Circuit-Digest/EdgeSense/X-CUBE-AI/App/gesture_nn_data_params.c

/**
  ******************************************************************************
  * @file    gesture_nn_data_params.c
  * @author  AST Embedded Analytics Research Platform
  * @date    2026-09-09T18:25:11+0530
  * @brief   AI Tool Automatic Code Generator for Embedded NN computing
  ******************************************************************************
  * Copyright (c) 2026 STMicroelectronics.
  * All rights reserved.
  *
  * This software is licensed under terms that can be found in the LICENSE file
  * in the root directory of this software component.
  * If no LICENSE file comes with this software, it is provided AS-IS.
  ******************************************************************************
  */

#include "gesture_nn_data_params.h"


/**  Activations Section  ****************************************************/
ai_handle g_gesture_nn_activations_table[1 + 2] = {
  AI_HANDLE_PTR(AI_MAGIC_MARKER),
  AI_HANDLE_PTR(NULL),
  AI_HANDLE_PTR(AI_MAGIC_MARKER),
};




/**  Weights Section  ********************************************************/
AI_ALIGNED(32)
const ai_u64 s_gesture_nn_weights_array_u64[5555] = {
  0xbd9bb6e83f14df5fU, 0xbd44f94dbe014eacU, 0xbd1a51113dd24123U, 0xbcd553593df90affU,
  0x3d6153e93e846b70U, 0xbe80cb583c3d5268U, 0xbdba1bb5bd9777c5U, 0x3f04b9d13dfc55edU,
  0x3bf491773cfa8731U, 0x3c975adabdd268f2U, 0x3b5d58443d19daa8U, 0xbcabd6d23dd9a1a6U,
  0xbdf308f43df9d848U, 0x3d3f640bbe3ce48dU, 0xbd5397b7bd332f07U, 0xbdb320333e840855U,
  0xbe5b8785be28c286U, 0x3c8ddacebdc4873fU, 0xbdaa8765bc5651dfU, 0xbdf82327be15460fU,
  0xbe254b2fbda32cbeU, 0xbdf089a43c857d3dU, 0x3eed92773d64c81dU, 0xbd1e19433d0020d6U,
  0xbc7e3dd33d837038U, 0xbd4f8ecd3ca2f35dU, 0xbe0b01223d28c61bU, 0xbe108f2dbce864bcU,
  0xbc1e46f0be5d9a9fU, 0xbe22220bbe2b8cdcU, 0x3d86b2283e4858aeU, 0xbdf83359bd084633U,
  0x3d54fd3c3c97acfaU, 0xbd25b1a83d59f5f9U, 0xbd9daabcbda7d2eaU, 0xbe33ac22be445608U,
  0xbd978d073d9d0282U, 0x3e51d1833e2aa8e3U, 0xbc61f3f13dbe44bfU, 0xbc63d6b13cd2e7aaU,
  0xbdb214d6bd10411eU, 0x3e357c22be07b82eU, 0xbe528ac13d65b2efU, 0xbe2cf3c0be321670U,
  0xbd25f38fbdc2d10aU, 0xbb11bd8e3e0925a0U, 0x3d5b9c55bc33f40bU, 0x3d4cb53e3dd98429U,
  0xbd83e82f3d1fc662U, 0xbe38ffffbd22bc52U, 0xbea0b887be0b6427U, 0xbe7a15d0be7af064U,
  0x3ec2225cbe8b4523U, 0xbcadbf9d3e7c4e67U, 0x3e2018c63d96a106U, 0x3b30cc8dbba42bc2U,
  0x3e92cd8e3d65e83dU, 0xbe041d51be29ddabU, 0xbe6e9141bea06f9aU, 0x3da25e0fbe8485bcU,
  0xbd5017433e99ad23U, 0xbbdf28b9bc7b145bU, 0x3e70a6a23d58f6e9U, 0x3e20848c3dab1275U,
  0x3e205ac9be1e68b7U, 0xbd530a87be8903d8U, 0xbe9e9ec0be6ac017U, 0x3cbd3068be810bc7U,
  0xbdc4b1d5bce5cf61U, 0x3d2197813c87fcf6U, 0x3d1fb6813d8118e7U, 0xbda204043cb005d6U,
  0xbc7b61c2bd0af53aU, 0xbdde2f35bd6bb885U, 0xbdf37e0ebdb69a86U, 0x3c859f963cab89a4U,
  0xbdec64313d5b8f71U, 0x3d9cfb8a3d6fb13dU, 0x3caa129c3c1a9bc7U, 0xbd8e4980bd1ee5bcU,
  0xbdb95145bc90474dU, 0xbdfdc86dbdbd1497U, 0xbbb6b49bbc889112U, 0xbd942b4c3d73a067U,
  0xbcb84b7c3cb400d0U, 0x3c9d65173d7c5fd4U, 0x3ce94b0fbd801503U, 0xbd6e76babbdaff04U,
  0xbe27f421bddade24U, 0xbe1eed30be110857U, 0x3e1f9dfc3e867a3bU, 0x3d933dd93df0f473U,
  0x3caa47093d4ffd83U, 0xbca2dc933dd88db2U, 0xbd7042943d83dd57U, 0xbe2dbe84bdfbccffU,
  0xbe2cb151be100aafU, 0x3e3519cebd15e8c3U, 0x3da1dadb3e33c0deU, 0x3cc22e2d3cf81887U,
  0x3e0bb2933dd55bd3U, 0x3cd4b1813db02daeU, 0xbe355672bded628bU, 0xbd9c5b8fbe4c7eacU,
  0x3aef856bbd76503cU, 0x3d085afe3e8d74dcU, 0x3dba91213dbad797U, 0x3db6013fbd548665U,
  0x3cd99d1f3ccd76b9U, 0xbc88aae9be070094U, 0xbe825a94be630f93U, 0xbe69157dbe33e0b7U,
  0x3dff146cbe2c41adU, 0x3cf884e03dc7510cU, 0x3e23b2433dda2873U, 0x3cb0a0b33df376b4U,
  0xbd9775673b8af4d6U, 0xbd3cf8a0bdbe190eU, 0xbd957e56bdcba0a5U, 0xbdecb5bebdb17824U,
  0x3d9837b73e96c7e6U, 0xbb82bf3f3e22d05bU, 0x3d7754f63e14c05cU, 0xbd424a873d6b1bb1U,
  0xbd9a4b44bd370cb8U, 0xbe50c98abdc45bb9U, 0xbdc91f6ebe2b674eU, 0x3dbc1987be1086ccU,
  0x3dec658b3dcad637U, 0x3ca6bd593cbae4e5U, 0x3d97c0133d975419U, 0x3d92751ebccdbc2eU,
  0xbdaaebb0be1318afU, 0xbe5f7e3bbe48beaeU, 0xbe6579bdbdd2de8bU, 0xbd86488fbe8cef7dU,
  0xbcf9b1f63df39c2aU, 0xbca99509bd4a1f07U, 0xbdeb21afbc96cdbcU, 0xbbd6a962bd2b63d0U,
  0x3e05407a3d0fee5eU, 0x3c8bf0843d7ae985U, 0xbee91858bcc95cedU, 0xbddda302bdc02ad8U,
  0xbca29313bdf88a7cU, 0xbdd670cabc9b0f23U, 0xbdc89d84bc63413fU, 0xbd13c175bc904147U,
  0xbd9f50283e2261abU, 0x3d5e6b203dbdb8eeU, 0xbe16168fbea39dd3U, 0xbe4fbb7ebe2874e5U,
  0xbd0f500bbe26e641U, 0xbe23f01abe02bcfcU, 0xbdf4898dbe393228U, 0x3d73f77fbe32da11U,
  0xbcfe56f8bd28355fU, 0xbc5420e63d888d9eU, 0x3d5af2993d5be35cU, 0x3d29aa3e3d911708U,
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
};


ai_handle g_gesture_nn_weights_table[1 + 2] = {
  AI_HANDLE_PTR(AI_MAGIC_MARKER),
  AI_HANDLE_PTR(s_gesture_nn_weights_array_u64),
  AI_HANDLE_PTR(AI_MAGIC_MARKER),
};
