Circuit-Digest/EdgeSense/X-CUBE-AI/App/posture_nn_data_params.c

/**
  ******************************************************************************
  * @file    posture_nn_data_params.c
  * @author  AST Embedded Analytics Research Platform
  * @date    2026-09-09T15:33:31+0530
  * @brief   AI Tool Automatic Code Generator for Embedded NN computing
  ******************************************************************************
  * Copyright (c) 2026 STMicroelectronics.
  * All rights reserved.
  *
  * This software is licensed under terms that can be found in the LICENSE file
  * in the root directory of this software component.
  * If no LICENSE file comes with this software, it is provided AS-IS.
  ******************************************************************************
  */

#include "posture_nn_data_params.h"


/**  Activations Section  ****************************************************/
ai_handle g_posture_nn_activations_table[1 + 2] = {
  AI_HANDLE_PTR(AI_MAGIC_MARKER),
  AI_HANDLE_PTR(NULL),
  AI_HANDLE_PTR(AI_MAGIC_MARKER),
};




/**  Weights Section  ********************************************************/
AI_ALIGNED(32)
const ai_u64 s_posture_nn_weights_array_u64[1343] = {
  0x3e1f9e293eea726cU, 0x3ec86b303de9e4e3U, 0x3f1459433d76b962U, 0x3f043da8bd12a9d7U,
  0x3efd3543be1ce815U, 0x3f22b9633e152a6bU, 0x3e579f75bdac4306U, 0x3f226002bf420823U,
  0x3f20f7a0bf2e1d6dU, 0xbebaef713e3f8c92U, 0xbeedce853e947dbcU, 0xbecca8f03e6467d3U,
  0xbed7bb653e190cc8U, 0xbe0a6b813d9f9190U, 0xbedd54933eac740bU, 0x3de2e219bd5258d9U,
  0x3f2a415ebde269c0U, 0x3efff3493e2b3ebeU, 0x3f0665603de452c5U, 0x3f1dffbfbecc9b92U,
  0x3f0a27e3bd807ae4U, 0xbd8828e73e0d1279U, 0x3ea0d94abef4ff45U, 0xbe2957af3e87964fU,
  0xbf4b20b53e3c6edaU, 0xbf749886bea4116dU, 0xbf90ed1cbe72ddfeU, 0x3e9c316ebdc03856U,
  0x3e6f4f5e3da30310U, 0xbd4a3d873ebc3302U, 0x3ea9ab16be4a4bf3U, 0x3e5490e3be077d8bU,
  0xbd1e058d3e413aa2U, 0x3db713023e744df1U, 0x3ec7669bbedb17eaU, 0xbe8df310be6e0c3bU,
  0xbefa684c3ea112d2U, 0xbf430ed03f0570c6U, 0xbf4fa0703dbe01f5U, 0xbf501ab93e085bc7U,
  0xbf182e263e41eea2U, 0xbf7952333dc2b288U, 0xbecc8bca3dd8374bU, 0xbe44b9debd88d878U,
  0xbeb76e4fbe000675U, 0x3e1925733d70ec3eU, 0x3ea22b61bf320acfU, 0x3e349cbbbf72ee9bU,
  0x3f2835da3d78340aU, 0x3ee6fcc13ac223c9U, 0x3ea948aebd8a04b6U, 0x3f5072f83db57964U,
  0x3f16ea033e6e8687U, 0x3f0c2763be82c2abU, 0xbe6e29dd3e8375eeU, 0xbe7429d8be42492eU,
  0xbee253b03d01bfd6U, 0xbec486e43e9c6062U, 0xbf06e50dbe913175U, 0xbf89e15a3d3f4183U,
  0xbf4c3f343dbf0d56U, 0xbf7b16863e928589U, 0xbf562c77be255263U, 0x3dbfa6e13e09128aU,
  0xbe6bacac3e5bf03aU, 0xbed9ae1b3e83d18cU, 0x3e069955be841b1cU, 0xbd7f76243e4a21fcU,
  0x3e4bf0ecbba43552U, 0x3ecb51ecbd0d453bU, 0x3f22af78bee9e80cU, 0x3e2ebeb2be6581d4U,
  0x3dc999c43f13ea3eU, 0x3e7365f33ea256f2U, 0xbec0ce6f3f3c7611U, 0xbecdfc3d3f53a581U,
  0xbc55c7a93d5519edU, 0xbcac2d353daab0bbU, 0xbd1f0b3b3d144f4cU, 0x3c2e12f23d9e22fdU,
  0x3d26abf6be00a9b3U, 0xbcc7079cbc85a4c4U, 0xbd4fbf7abdc40968U, 0x3c96612d3b3fd5c0U,
  0x3dc92d23bb2acc00U, 0x3d531316bdef5613U, 0xbd3baad73d28ff92U, 0xbdc1df303d582826U,
  0x3d966304bdf9c943U, 0xbda08a4f3da2a1e4U, 0xbd74574ebcabb1b1U, 0xbdf1d5f1bd6b565aU,
  0x3d1f40aebd3a69ecU, 0xbd3aefb8bd4bd058U, 0xbd9add9fbdce616fU, 0xbd612f5ebdb5775aU,
  0xbd987ce03ceb2484U, 0xbdcfabf5bd3c832eU, 0x3d76b622bdcade7cU, 0xbda6e71c3abf5148U,
  0xbdba99153dc9587bU, 0xbd3a863e3bd36b3aU, 0xbbcf53903bf36894U, 0xbd80ac30bab42a1cU,
  0x3d95d1a53b089be0U, 0xbc9450403dac45dfU, 0x3d087c19bd322fecU, 0xbc9886acbd37c4ebU,
  0xbdb026683ce68efcU, 0x3db303433d3e0142U, 0x3dbbcdefbd40a73cU, 0xbc88379e3cb7afecU,
  0x3e81243cba6f0596U, 0xbd671ef3be2f3af8U, 0x3dac1eb13e2ee6f0U, 0x3ed55dff3e12bb11U,
  0xbd92ce5e3e4e311dU, 0x3d562a0c3d4c7722U, 0x3d598e6c3daff7e6U, 0x3d159bfb3d80c17aU,
  0x3c5cb670baad6810U, 0x3e7a2c2a3d197328U, 0x3dcacc2f3e0b4733U, 0x3d36149c3da268dbU,
  0xbe7a43423c33cb97U, 0xbc53f8d3bd7eb177U, 0x3d26fcd03d1b2a16U, 0x3e0be258be5bb857U,
  0xbe83c33a3e178639U, 0x3e7501ce3af9c1fcU, 0xbde724613d80e987U, 0x3e2cf4f2bdb215b1U,
  0xbd7bb11abdc859d8U, 0x3d287ce13d7e66d4U, 0xbd5b4720be263a92U, 0x3e0159343e052b74U,
  0x3e692d57bd9c94c5U, 0xbd0c6d633d8dccfbU, 0x3ee8f8493ec5f783U, 0xbbc04ab53c87d2afU,
  0xbcac57f5bdeefc79U, 0x3dc2afdc3df367c7U, 0xbd88fecebe14d918U, 0xbdd04bd83df95995U,
  0x3e0bd28e3dbe0b9cU, 0x3da124e4be53e4dcU, 0x3c59cb563d4b7039U, 0x3de9f2483e33da65U,
  0x3d8fd487bde5085bU, 0x3d1941bdbe1b794dU, 0x3d85b39e3e1eea57U, 0xbdb2bafcbd157b94U,
  0xbd532cea3d041d58U, 0x3d89f79d3e2d497aU, 0xbd9c0cd13d866ba6U, 0xbcbb045c3c7e7761U,
  0x3d1c7ce63e154295U, 0xbde64e09be6db519U, 0xbd6834a9be346318U, 0xbceca2fd3d223e3dU,
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
};


ai_handle g_posture_nn_weights_table[1 + 2] = {
  AI_HANDLE_PTR(AI_MAGIC_MARKER),
  AI_HANDLE_PTR(s_posture_nn_weights_array_u64),
  AI_HANDLE_PTR(AI_MAGIC_MARKER),
};
