Circuit-Digest/EdgeSense/X-CUBE-AI/App/surface_nn.c

/**
  ******************************************************************************
  * @file    surface_nn.c
  * @author  AST Embedded Analytics Research Platform
  * @date    2026-09-09T16:02:45+0530
  * @brief   AI Tool Automatic Code Generator for Embedded NN computing
  ******************************************************************************
  * @attention
  *
  * Copyright (c) 2026 STMicroelectronics.
  * All rights reserved.
  *
  * This software is licensed under terms that can be found in the LICENSE file
  * in the root directory of this software component.
  * If no LICENSE file comes with this software, it is provided AS-IS.
  ******************************************************************************
  */


#include "surface_nn.h"
#include "surface_nn_data.h"

#include "ai_platform.h"
#include "ai_platform_interface.h"
#include "ai_math_helpers.h"

#include "core_common.h"
#include "core_convert.h"

#include "layers.h"



#undef AI_NET_OBJ_INSTANCE
#define AI_NET_OBJ_INSTANCE g_surface_nn
 
#undef AI_SURFACE_NN_MODEL_SIGNATURE
#define AI_SURFACE_NN_MODEL_SIGNATURE     "0xba809538a7b4a5e3b27630bb6a6ce773"

#ifndef AI_TOOLS_REVISION_ID
#define AI_TOOLS_REVISION_ID     ""
#endif

#undef AI_TOOLS_DATE_TIME
#define AI_TOOLS_DATE_TIME   "2026-09-09T16:02:45+0530"

#undef AI_TOOLS_COMPILE_TIME
#define AI_TOOLS_COMPILE_TIME    __DATE__ " " __TIME__

#undef AI_SURFACE_NN_N_BATCHES
#define AI_SURFACE_NN_N_BATCHES         (1)

static ai_ptr g_surface_nn_activations_map[1] = AI_C_ARRAY_INIT;
static ai_ptr g_surface_nn_weights_map[1] = AI_C_ARRAY_INIT;



/**  Array declarations section  **********************************************/
/* Array#0 */
AI_ARRAY_OBJ_DECLARE(
  input_canonical_output_array, AI_ARRAY_FORMAT_FLOAT|AI_FMT_FLAG_IS_IO,
  NULL, NULL, 16, AI_STATIC)

/* Array#1 */
AI_ARRAY_OBJ_DECLARE(
  _conv1_Conv_output_0_output_array, AI_ARRAY_FORMAT_FLOAT,
  NULL, NULL, 64, AI_STATIC)

/* Array#2 */
AI_ARRAY_OBJ_DECLARE(
  _conv2_Conv_output_0_output_array, AI_ARRAY_FORMAT_FLOAT,
  NULL, NULL, 64, AI_STATIC)

/* Array#3 */
AI_ARRAY_OBJ_DECLARE(
  _fc1_Gemm_output_0_output_array, AI_ARRAY_FORMAT_FLOAT,
  NULL, NULL, 16, AI_STATIC)

/* Array#4 */
AI_ARRAY_OBJ_DECLARE(
  _relu3_Relu_output_0_output_array, AI_ARRAY_FORMAT_FLOAT,
  NULL, NULL, 16, AI_STATIC)

/* Array#5 */
AI_ARRAY_OBJ_DECLARE(
  output_logits_output_array, AI_ARRAY_FORMAT_FLOAT|AI_FMT_FLAG_IS_IO,
  NULL, NULL, 4, AI_STATIC)

/* Array#6 */
AI_ARRAY_OBJ_DECLARE(
  _conv1_Conv_output_0_weights_array, AI_ARRAY_FORMAT_FLOAT,
  NULL, NULL, 24, AI_STATIC)

/* Array#7 */
AI_ARRAY_OBJ_DECLARE(
  _conv1_Conv_output_0_bias_array, AI_ARRAY_FORMAT_FLOAT,
  NULL, NULL, 8, AI_STATIC)

/* Array#8 */
AI_ARRAY_OBJ_DECLARE(
  _conv2_Conv_output_0_weights_array, AI_ARRAY_FORMAT_FLOAT,
  NULL, NULL, 384, AI_STATIC)

/* Array#9 */
AI_ARRAY_OBJ_DECLARE(
  _conv2_Conv_output_0_bias_array, AI_ARRAY_FORMAT_FLOAT,
  NULL, NULL, 16, AI_STATIC)

/* Array#10 */
AI_ARRAY_OBJ_DECLARE(
  _fc1_Gemm_output_0_weights_array, AI_ARRAY_FORMAT_FLOAT,
  NULL, NULL, 1024, AI_STATIC)

/* Array#11 */
AI_ARRAY_OBJ_DECLARE(
  _fc1_Gemm_output_0_bias_array, AI_ARRAY_FORMAT_FLOAT,
  NULL, NULL, 16, AI_STATIC)

/* Array#12 */
AI_ARRAY_OBJ_DECLARE(
  output_logits_weights_array, AI_ARRAY_FORMAT_FLOAT,
  NULL, NULL, 64, AI_STATIC)

/* Array#13 */
AI_ARRAY_OBJ_DECLARE(
  output_logits_bias_array, AI_ARRAY_FORMAT_FLOAT,
  NULL, NULL, 4, AI_STATIC)

/* Array#14 */
AI_ARRAY_OBJ_DECLARE(
  _conv1_Conv_output_0_scratch0_array, AI_ARRAY_FORMAT_FLOAT,
  NULL, NULL, 3, AI_STATIC)

/* Array#15 */
AI_ARRAY_OBJ_DECLARE(
  _conv1_Conv_output_0_scratch1_array, AI_ARRAY_FORMAT_FLOAT,
  NULL, NULL, 16, AI_STATIC)

/* Array#16 */
AI_ARRAY_OBJ_DECLARE(
  _conv2_Conv_output_0_scratch0_array, AI_ARRAY_FORMAT_FLOAT,
  NULL, NULL, 24, AI_STATIC)

/* Array#17 */
AI_ARRAY_OBJ_DECLARE(
  _conv2_Conv_output_0_scratch1_array, AI_ARRAY_FORMAT_FLOAT,
  NULL, NULL, 32, AI_STATIC)

/**  Tensor declarations section  *********************************************/
/* Tensor #0 */
AI_TENSOR_OBJ_DECLARE(
  _conv1_Conv_output_0_bias, AI_STATIC,
  0, 0x0,
  AI_SHAPE_INIT(4, 1, 8, 1, 1), AI_STRIDE_INIT(4, 4, 4, 32, 32),
  1, &_conv1_Conv_output_0_bias_array, NULL)

/* Tensor #1 */
AI_TENSOR_OBJ_DECLARE(
  _conv1_Conv_output_0_output, AI_STATIC,
  1, 0x0,
  AI_SHAPE_INIT(4, 1, 8, 1, 8), AI_STRIDE_INIT(4, 4, 4, 32, 32),
  1, &_conv1_Conv_output_0_output_array, NULL)

/* Tensor #2 */
AI_TENSOR_OBJ_DECLARE(
  _conv1_Conv_output_0_scratch0, AI_STATIC,
  2, 0x0,
  AI_SHAPE_INIT(4, 1, 1, 1, 3), AI_STRIDE_INIT(4, 4, 4, 4, 4),
  1, &_conv1_Conv_output_0_scratch0_array, NULL)

/* Tensor #3 */
AI_TENSOR_OBJ_DECLARE(
  _conv1_Conv_output_0_scratch1, AI_STATIC,
  3, 0x0,
  AI_SHAPE_INIT(4, 1, 8, 1, 2), AI_STRIDE_INIT(4, 4, 4, 32, 32),
  1, &_conv1_Conv_output_0_scratch1_array, NULL)

/* Tensor #4 */
AI_TENSOR_OBJ_DECLARE(
  _conv1_Conv_output_0_weights, AI_STATIC,
  4, 0x0,
  AI_SHAPE_INIT(4, 1, 1, 3, 8), AI_STRIDE_INIT(4, 4, 4, 32, 32),
  1, &_conv1_Conv_output_0_weights_array, NULL)

/* Tensor #5 */
AI_TENSOR_OBJ_DECLARE(
  _conv2_Conv_output_0_bias, AI_STATIC,
  5, 0x0,
  AI_SHAPE_INIT(4, 1, 16, 1, 1), AI_STRIDE_INIT(4, 4, 4, 64, 64),
  1, &_conv2_Conv_output_0_bias_array, NULL)

/* Tensor #6 */
AI_TENSOR_OBJ_DECLARE(
  _conv2_Conv_output_0_output, AI_STATIC,
  6, 0x0,
  AI_SHAPE_INIT(4, 1, 16, 1, 4), AI_STRIDE_INIT(4, 4, 4, 64, 64),
  1, &_conv2_Conv_output_0_output_array, NULL)

/* Tensor #7 */
AI_TENSOR_OBJ_DECLARE(
  _conv2_Conv_output_0_output0, AI_STATIC,
  7, 0x0,
  AI_SHAPE_INIT(4, 1, 64, 1, 1), AI_STRIDE_INIT(4, 4, 4, 256, 256),
  1, &_conv2_Conv_output_0_output_array, NULL)

/* Tensor #8 */
AI_TENSOR_OBJ_DECLARE(
  _conv2_Conv_output_0_scratch0, AI_STATIC,
  8, 0x0,
  AI_SHAPE_INIT(4, 1, 8, 1, 3), AI_STRIDE_INIT(4, 4, 4, 32, 32),
  1, &_conv2_Conv_output_0_scratch0_array, NULL)

/* Tensor #9 */
AI_TENSOR_OBJ_DECLARE(
  _conv2_Conv_output_0_scratch1, AI_STATIC,
  9, 0x0,
  AI_SHAPE_INIT(4, 1, 16, 1, 2), AI_STRIDE_INIT(4, 4, 4, 64, 64),
  1, &_conv2_Conv_output_0_scratch1_array, NULL)

/* Tensor #10 */
AI_TENSOR_OBJ_DECLARE(
  _conv2_Conv_output_0_weights, AI_STATIC,
  10, 0x0,
  AI_SHAPE_INIT(4, 8, 1, 3, 16), AI_STRIDE_INIT(4, 4, 32, 512, 512),
  1, &_conv2_Conv_output_0_weights_array, NULL)

/* Tensor #11 */
AI_TENSOR_OBJ_DECLARE(
  _fc1_Gemm_output_0_bias, AI_STATIC,
  11, 0x0,
  AI_SHAPE_INIT(4, 1, 16, 1, 1), AI_STRIDE_INIT(4, 4, 4, 64, 64),
  1, &_fc1_Gemm_output_0_bias_array, NULL)

/* Tensor #12 */
AI_TENSOR_OBJ_DECLARE(
  _fc1_Gemm_output_0_output, AI_STATIC,
  12, 0x0,
  AI_SHAPE_INIT(4, 1, 16, 1, 1), AI_STRIDE_INIT(4, 4, 4, 64, 64),
  1, &_fc1_Gemm_output_0_output_array, NULL)

/* Tensor #13 */
AI_TENSOR_OBJ_DECLARE(
  _fc1_Gemm_output_0_weights, AI_STATIC,
  13, 0x0,
  AI_SHAPE_INIT(4, 64, 16, 1, 1), AI_STRIDE_INIT(4, 4, 256, 4096, 4096),
  1, &_fc1_Gemm_output_0_weights_array, NULL)

/* Tensor #14 */
AI_TENSOR_OBJ_DECLARE(
  _relu3_Relu_output_0_output, AI_STATIC,
  14, 0x0,
  AI_SHAPE_INIT(4, 1, 16, 1, 1), AI_STRIDE_INIT(4, 4, 4, 64, 64),
  1, &_relu3_Relu_output_0_output_array, NULL)

/* Tensor #15 */
AI_TENSOR_OBJ_DECLARE(
  input_canonical_output, AI_STATIC,
  15, 0x0,
  AI_SHAPE_INIT(4, 1, 1, 1, 16), AI_STRIDE_INIT(4, 4, 4, 4, 4),
  1, &input_canonical_output_array, NULL)

/* Tensor #16 */
AI_TENSOR_OBJ_DECLARE(
  output_logits_bias, AI_STATIC,
  16, 0x0,
  AI_SHAPE_INIT(4, 1, 4, 1, 1), AI_STRIDE_INIT(4, 4, 4, 16, 16),
  1, &output_logits_bias_array, NULL)

/* Tensor #17 */
AI_TENSOR_OBJ_DECLARE(
  output_logits_output, AI_STATIC,
  17, 0x0,
  AI_SHAPE_INIT(4, 1, 4, 1, 1), AI_STRIDE_INIT(4, 4, 4, 16, 16),
  1, &output_logits_output_array, NULL)

/* Tensor #18 */
AI_TENSOR_OBJ_DECLARE(
  output_logits_weights, AI_STATIC,
  18, 0x0,
  AI_SHAPE_INIT(4, 16, 4, 1, 1), AI_STRIDE_INIT(4, 4, 64, 256, 256),
  1, &output_logits_weights_array, NULL)



/**  Layer declarations section  **********************************************/


AI_TENSOR_CHAIN_OBJ_DECLARE(
  output_logits_chain, AI_STATIC_CONST, 4,
  AI_TENSOR_LIST_OBJ_INIT(AI_FLAG_NONE, 1, &_relu3_Relu_output_0_output),
  AI_TENSOR_LIST_OBJ_INIT(AI_FLAG_NONE, 1, &output_logits_output),
  AI_TENSOR_LIST_OBJ_INIT(AI_FLAG_NONE, 2, &output_logits_weights, &output_logits_bias),
  AI_TENSOR_LIST_OBJ_EMPTY
)

AI_LAYER_OBJ_DECLARE(
  output_logits_layer, 10,
  DENSE_TYPE, 0x0, NULL,
  dense, forward_dense,
  &output_logits_chain,
  NULL, &output_logits_layer, AI_STATIC, 
)

AI_TENSOR_CHAIN_OBJ_DECLARE(
  _relu3_Relu_output_0_chain, AI_STATIC_CONST, 4,
  AI_TENSOR_LIST_OBJ_INIT(AI_FLAG_NONE, 1, &_fc1_Gemm_output_0_output),
  AI_TENSOR_LIST_OBJ_INIT(AI_FLAG_NONE, 1, &_relu3_Relu_output_0_output),
  AI_TENSOR_LIST_OBJ_EMPTY,
  AI_TENSOR_LIST_OBJ_EMPTY
)

AI_LAYER_OBJ_DECLARE(
  _relu3_Relu_output_0_layer, 9,
  NL_TYPE, 0x0, NULL,
  nl, forward_relu,
  &_relu3_Relu_output_0_chain,
  NULL, &output_logits_layer, AI_STATIC, 
  .nl_params = NULL, 
)

AI_TENSOR_CHAIN_OBJ_DECLARE(
  _fc1_Gemm_output_0_chain, AI_STATIC_CONST, 4,
  AI_TENSOR_LIST_OBJ_INIT(AI_FLAG_NONE, 1, &_conv2_Conv_output_0_output0),
  AI_TENSOR_LIST_OBJ_INIT(AI_FLAG_NONE, 1, &_fc1_Gemm_output_0_output),
  AI_TENSOR_LIST_OBJ_INIT(AI_FLAG_NONE, 2, &_fc1_Gemm_output_0_weights, &_fc1_Gemm_output_0_bias),
  AI_TENSOR_LIST_OBJ_EMPTY
)

AI_LAYER_OBJ_DECLARE(
  _fc1_Gemm_output_0_layer, 8,
  DENSE_TYPE, 0x0, NULL,
  dense, forward_dense,
  &_fc1_Gemm_output_0_chain,
  NULL, &_relu3_Relu_output_0_layer, AI_STATIC, 
)

AI_TENSOR_CHAIN_OBJ_DECLARE(
  _conv2_Conv_output_0_chain, AI_STATIC_CONST, 4,
  AI_TENSOR_LIST_OBJ_INIT(AI_FLAG_NONE, 1, &_conv1_Conv_output_0_output),
  AI_TENSOR_LIST_OBJ_INIT(AI_FLAG_NONE, 1, &_conv2_Conv_output_0_output),
  AI_TENSOR_LIST_OBJ_INIT(AI_FLAG_NONE, 3, &_conv2_Conv_output_0_weights, &_conv2_Conv_output_0_bias, NULL),
  AI_TENSOR_LIST_OBJ_INIT(AI_FLAG_NONE, 2, &_conv2_Conv_output_0_scratch0, &_conv2_Conv_output_0_scratch1)
)

AI_LAYER_OBJ_DECLARE(
  _conv2_Conv_output_0_layer, 6,
  OPTIMIZED_CONV2D_TYPE, 0x0, NULL,
  conv2d_nl_pool, forward_conv2d_if32of32wf32_nl_pool,
  &_conv2_Conv_output_0_chain,
  NULL, &_fc1_Gemm_output_0_layer, AI_STATIC, 
  .groups = 1, 
  .nl_params = NULL, 
  .nl_func = AI_HANDLE_PTR(forward_lite_nl_relu_if32of32), 
  .filter_stride = AI_SHAPE_2D_INIT(1, 1), 
  .dilation = AI_SHAPE_2D_INIT(1, 1), 
  .filter_pad = AI_SHAPE_INIT(4, 1, 0, 1, 0), 
  .pool_size = AI_SHAPE_2D_INIT(1, 2), 
  .pool_stride = AI_SHAPE_2D_INIT(1, 2), 
  .pool_pad = AI_SHAPE_INIT(4, 0, 0, 0, 0), 
  .pool_func = AI_HANDLE_PTR(pool_func_mp_array_f32), 
  .in_ch_format = AI_LAYER_FORMAT_CHANNEL_LAST_SAME, 
  .out_ch_format = AI_LAYER_FORMAT_CHANNEL_LAST_VALID, 
)

AI_TENSOR_CHAIN_OBJ_DECLARE(
  _conv1_Conv_output_0_chain, AI_STATIC_CONST, 4,
  AI_TENSOR_LIST_OBJ_INIT(AI_FLAG_NONE, 1, &input_canonical_output),
  AI_TENSOR_LIST_OBJ_INIT(AI_FLAG_NONE, 1, &_conv1_Conv_output_0_output),
  AI_TENSOR_LIST_OBJ_INIT(AI_FLAG_NONE, 3, &_conv1_Conv_output_0_weights, &_conv1_Conv_output_0_bias, NULL),
  AI_TENSOR_LIST_OBJ_INIT(AI_FLAG_NONE, 2, &_conv1_Conv_output_0_scratch0, &_conv1_Conv_output_0_scratch1)
)

AI_LAYER_OBJ_DECLARE(
  _conv1_Conv_output_0_layer, 3,
  OPTIMIZED_CONV2D_TYPE, 0x0, NULL,
  conv2d_nl_pool, forward_conv2d_if32of32wf32_nl_pool,
  &_conv1_Conv_output_0_chain,
  NULL, &_conv2_Conv_output_0_layer, AI_STATIC, 
  .groups = 1, 
  .nl_params = NULL, 
  .nl_func = AI_HANDLE_PTR(forward_lite_nl_relu_if32of32), 
  .filter_stride = AI_SHAPE_2D_INIT(1, 1), 
  .dilation = AI_SHAPE_2D_INIT(1, 1), 
  .filter_pad = AI_SHAPE_INIT(4, 1, 0, 1, 0), 
  .pool_size = AI_SHAPE_2D_INIT(1, 2), 
  .pool_stride = AI_SHAPE_2D_INIT(1, 2), 
  .pool_pad = AI_SHAPE_INIT(4, 0, 0, 0, 0), 
  .pool_func = AI_HANDLE_PTR(pool_func_mp_array_f32), 
  .in_ch_format = AI_LAYER_FORMAT_CHANNEL_LAST_SAME, 
  .out_ch_format = AI_LAYER_FORMAT_CHANNEL_LAST_VALID, 
)


#if (AI_TOOLS_API_VERSION < AI_TOOLS_API_VERSION_1_5)

AI_NETWORK_OBJ_DECLARE(
  AI_NET_OBJ_INSTANCE, AI_STATIC,
  AI_BUFFER_INIT(AI_FLAG_NONE,  AI_BUFFER_FORMAT_U8,
    AI_BUFFER_SHAPE_INIT(AI_SHAPE_BCWH, 4, 1, 6160, 1, 1),
    6160, NULL, NULL),
  AI_BUFFER_INIT(AI_FLAG_NONE,  AI_BUFFER_FORMAT_U8,
    AI_BUFFER_SHAPE_INIT(AI_SHAPE_BCWH, 4, 1, 704, 1, 1),
    704, NULL, NULL),
  AI_TENSOR_LIST_IO_OBJ_INIT(AI_FLAG_NONE, AI_SURFACE_NN_IN_NUM, &input_canonical_output),
  AI_TENSOR_LIST_IO_OBJ_INIT(AI_FLAG_NONE, AI_SURFACE_NN_OUT_NUM, &output_logits_output),
  &_conv1_Conv_output_0_layer, 0xb18cfe6e, NULL)

#else

AI_NETWORK_OBJ_DECLARE(
  AI_NET_OBJ_INSTANCE, AI_STATIC,
  AI_BUFFER_ARRAY_OBJ_INIT_STATIC(
  	AI_FLAG_NONE, 1,
    AI_BUFFER_INIT(AI_FLAG_NONE,  AI_BUFFER_FORMAT_U8,
      AI_BUFFER_SHAPE_INIT(AI_SHAPE_BCWH, 4, 1, 6160, 1, 1),
      6160, NULL, NULL)
  ),
  AI_BUFFER_ARRAY_OBJ_INIT_STATIC(
  	AI_FLAG_NONE, 1,
    AI_BUFFER_INIT(AI_FLAG_NONE,  AI_BUFFER_FORMAT_U8,
      AI_BUFFER_SHAPE_INIT(AI_SHAPE_BCWH, 4, 1, 704, 1, 1),
      704, NULL, NULL)
  ),
  AI_TENSOR_LIST_IO_OBJ_INIT(AI_FLAG_NONE, AI_SURFACE_NN_IN_NUM, &input_canonical_output),
  AI_TENSOR_LIST_IO_OBJ_INIT(AI_FLAG_NONE, AI_SURFACE_NN_OUT_NUM, &output_logits_output),
  &_conv1_Conv_output_0_layer, 0xb18cfe6e, NULL)

#endif	/*(AI_TOOLS_API_VERSION < AI_TOOLS_API_VERSION_1_5)*/



/******************************************************************************/
AI_DECLARE_STATIC
ai_bool surface_nn_configure_activations(
  ai_network* net_ctx, const ai_network_params* params)
{
  AI_ASSERT(net_ctx)

  if (ai_platform_get_activations_map(g_surface_nn_activations_map, 1, params)) {
    /* Updating activations (byte) offsets */
    
    input_canonical_output_array.data = AI_PTR(g_surface_nn_activations_map[0] + 84);
    input_canonical_output_array.data_start = AI_PTR(g_surface_nn_activations_map[0] + 84);
    _conv1_Conv_output_0_scratch0_array.data = AI_PTR(g_surface_nn_activations_map[0] + 148);
    _conv1_Conv_output_0_scratch0_array.data_start = AI_PTR(g_surface_nn_activations_map[0] + 148);
    _conv1_Conv_output_0_scratch1_array.data = AI_PTR(g_surface_nn_activations_map[0] + 160);
    _conv1_Conv_output_0_scratch1_array.data_start = AI_PTR(g_surface_nn_activations_map[0] + 160);
    _conv1_Conv_output_0_output_array.data = AI_PTR(g_surface_nn_activations_map[0] + 224);
    _conv1_Conv_output_0_output_array.data_start = AI_PTR(g_surface_nn_activations_map[0] + 224);
    _conv2_Conv_output_0_scratch0_array.data = AI_PTR(g_surface_nn_activations_map[0] + 480);
    _conv2_Conv_output_0_scratch0_array.data_start = AI_PTR(g_surface_nn_activations_map[0] + 480);
    _conv2_Conv_output_0_scratch1_array.data = AI_PTR(g_surface_nn_activations_map[0] + 576);
    _conv2_Conv_output_0_scratch1_array.data_start = AI_PTR(g_surface_nn_activations_map[0] + 576);
    _conv2_Conv_output_0_output_array.data = AI_PTR(g_surface_nn_activations_map[0] + 0);
    _conv2_Conv_output_0_output_array.data_start = AI_PTR(g_surface_nn_activations_map[0] + 0);
    _fc1_Gemm_output_0_output_array.data = AI_PTR(g_surface_nn_activations_map[0] + 256);
    _fc1_Gemm_output_0_output_array.data_start = AI_PTR(g_surface_nn_activations_map[0] + 256);
    _relu3_Relu_output_0_output_array.data = AI_PTR(g_surface_nn_activations_map[0] + 0);
    _relu3_Relu_output_0_output_array.data_start = AI_PTR(g_surface_nn_activations_map[0] + 0);
    output_logits_output_array.data = AI_PTR(g_surface_nn_activations_map[0] + 64);
    output_logits_output_array.data_start = AI_PTR(g_surface_nn_activations_map[0] + 64);
    return true;
  }
  AI_ERROR_TRAP(net_ctx, INIT_FAILED, NETWORK_ACTIVATIONS);
  return false;
}




/******************************************************************************/
AI_DECLARE_STATIC
ai_bool surface_nn_configure_weights(
  ai_network* net_ctx, const ai_network_params* params)
{
  AI_ASSERT(net_ctx)

  if (ai_platform_get_weights_map(g_surface_nn_weights_map, 1, params)) {
    /* Updating weights (byte) offsets */
    
    _conv1_Conv_output_0_weights_array.format |= AI_FMT_FLAG_CONST;
    _conv1_Conv_output_0_weights_array.data = AI_PTR(g_surface_nn_weights_map[0] + 0);
    _conv1_Conv_output_0_weights_array.data_start = AI_PTR(g_surface_nn_weights_map[0] + 0);
    _conv1_Conv_output_0_bias_array.format |= AI_FMT_FLAG_CONST;
    _conv1_Conv_output_0_bias_array.data = AI_PTR(g_surface_nn_weights_map[0] + 96);
    _conv1_Conv_output_0_bias_array.data_start = AI_PTR(g_surface_nn_weights_map[0] + 96);
    _conv2_Conv_output_0_weights_array.format |= AI_FMT_FLAG_CONST;
    _conv2_Conv_output_0_weights_array.data = AI_PTR(g_surface_nn_weights_map[0] + 128);
    _conv2_Conv_output_0_weights_array.data_start = AI_PTR(g_surface_nn_weights_map[0] + 128);
    _conv2_Conv_output_0_bias_array.format |= AI_FMT_FLAG_CONST;
    _conv2_Conv_output_0_bias_array.data = AI_PTR(g_surface_nn_weights_map[0] + 1664);
    _conv2_Conv_output_0_bias_array.data_start = AI_PTR(g_surface_nn_weights_map[0] + 1664);
    _fc1_Gemm_output_0_weights_array.format |= AI_FMT_FLAG_CONST;
    _fc1_Gemm_output_0_weights_array.data = AI_PTR(g_surface_nn_weights_map[0] + 1728);
    _fc1_Gemm_output_0_weights_array.data_start = AI_PTR(g_surface_nn_weights_map[0] + 1728);
    _fc1_Gemm_output_0_bias_array.format |= AI_FMT_FLAG_CONST;
    _fc1_Gemm_output_0_bias_array.data = AI_PTR(g_surface_nn_weights_map[0] + 5824);
    _fc1_Gemm_output_0_bias_array.data_start = AI_PTR(g_surface_nn_weights_map[0] + 5824);
    output_logits_weights_array.format |= AI_FMT_FLAG_CONST;
    output_logits_weights_array.data = AI_PTR(g_surface_nn_weights_map[0] + 5888);
    output_logits_weights_array.data_start = AI_PTR(g_surface_nn_weights_map[0] + 5888);
    output_logits_bias_array.format |= AI_FMT_FLAG_CONST;
    output_logits_bias_array.data = AI_PTR(g_surface_nn_weights_map[0] + 6144);
    output_logits_bias_array.data_start = AI_PTR(g_surface_nn_weights_map[0] + 6144);
    return true;
  }
  AI_ERROR_TRAP(net_ctx, INIT_FAILED, NETWORK_WEIGHTS);
  return false;
}


/**  PUBLIC APIs SECTION  *****************************************************/



AI_DEPRECATED
AI_API_ENTRY
ai_bool ai_surface_nn_get_info(
  ai_handle network, ai_network_report* report)
{
  ai_network* net_ctx = AI_NETWORK_ACQUIRE_CTX(network);

  if (report && net_ctx)
  {
    ai_network_report r = {
      .model_name        = AI_SURFACE_NN_MODEL_NAME,
      .model_signature   = AI_SURFACE_NN_MODEL_SIGNATURE,
      .model_datetime    = AI_TOOLS_DATE_TIME,
      
      .compile_datetime  = AI_TOOLS_COMPILE_TIME,
      
      .runtime_revision  = ai_platform_runtime_get_revision(),
      .runtime_version   = ai_platform_runtime_get_version(),

      .tool_revision     = AI_TOOLS_REVISION_ID,
      .tool_version      = {AI_TOOLS_VERSION_MAJOR, AI_TOOLS_VERSION_MINOR,
                            AI_TOOLS_VERSION_MICRO, 0x0},
      .tool_api_version  = AI_STRUCT_INIT,

      .api_version            = ai_platform_api_get_version(),
      .interface_api_version  = ai_platform_interface_api_get_version(),
      
      .n_macc            = 5116,
      .n_inputs          = 0,
      .inputs            = NULL,
      .n_outputs         = 0,
      .outputs           = NULL,
      .params            = AI_STRUCT_INIT,
      .activations       = AI_STRUCT_INIT,
      .n_nodes           = 0,
      .signature         = 0xb18cfe6e,
    };

    if (!ai_platform_api_get_network_report(network, &r)) return false;

    *report = r;
    return true;
  }
  return false;
}



AI_API_ENTRY
ai_bool ai_surface_nn_get_report(
  ai_handle network, ai_network_report* report)
{
  ai_network* net_ctx = AI_NETWORK_ACQUIRE_CTX(network);

  if (report && net_ctx)
  {
    ai_network_report r = {
      .model_name        = AI_SURFACE_NN_MODEL_NAME,
      .model_signature   = AI_SURFACE_NN_MODEL_SIGNATURE,
      .model_datetime    = AI_TOOLS_DATE_TIME,
      
      .compile_datetime  = AI_TOOLS_COMPILE_TIME,
      
      .runtime_revision  = ai_platform_runtime_get_revision(),
      .runtime_version   = ai_platform_runtime_get_version(),

      .tool_revision     = AI_TOOLS_REVISION_ID,
      .tool_version      = {AI_TOOLS_VERSION_MAJOR, AI_TOOLS_VERSION_MINOR,
                            AI_TOOLS_VERSION_MICRO, 0x0},
      .tool_api_version  = AI_STRUCT_INIT,

      .api_version            = ai_platform_api_get_version(),
      .interface_api_version  = ai_platform_interface_api_get_version(),
      
      .n_macc            = 5116,
      .n_inputs          = 0,
      .inputs            = NULL,
      .n_outputs         = 0,
      .outputs           = NULL,
      .map_signature     = AI_MAGIC_SIGNATURE,
      .map_weights       = AI_STRUCT_INIT,
      .map_activations   = AI_STRUCT_INIT,
      .n_nodes           = 0,
      .signature         = 0xb18cfe6e,
    };

    if (!ai_platform_api_get_network_report(network, &r)) return false;

    *report = r;
    return true;
  }
  return false;
}


AI_API_ENTRY
ai_error ai_surface_nn_get_error(ai_handle network)
{
  return ai_platform_network_get_error(network);
}


AI_API_ENTRY
ai_error ai_surface_nn_create(
  ai_handle* network, const ai_buffer* network_config)
{
  return ai_platform_network_create(
    network, network_config, 
    AI_CONTEXT_OBJ(&AI_NET_OBJ_INSTANCE),
    AI_TOOLS_API_VERSION_MAJOR, AI_TOOLS_API_VERSION_MINOR, AI_TOOLS_API_VERSION_MICRO);
}


AI_API_ENTRY
ai_error ai_surface_nn_create_and_init(
  ai_handle* network, const ai_handle activations[], const ai_handle weights[])
{
  ai_error err;
  ai_network_params params;

  err = ai_surface_nn_create(network, AI_SURFACE_NN_DATA_CONFIG);
  if (err.type != AI_ERROR_NONE) {
    return err;
  }
  
  if (ai_surface_nn_data_params_get(&params) != true) {
    err = ai_surface_nn_get_error(*network);
    return err;
  }
#if defined(AI_SURFACE_NN_DATA_ACTIVATIONS_COUNT)
  /* set the addresses of the activations buffers */
  for (ai_u16 idx=0; activations && idx<params.map_activations.size; idx++) {
    AI_BUFFER_ARRAY_ITEM_SET_ADDRESS(&params.map_activations, idx, activations[idx]);
  }
#endif
#if defined(AI_SURFACE_NN_DATA_WEIGHTS_COUNT)
  /* set the addresses of the weight buffers */
  for (ai_u16 idx=0; weights && idx<params.map_weights.size; idx++) {
    AI_BUFFER_ARRAY_ITEM_SET_ADDRESS(&params.map_weights, idx, weights[idx]);
  }
#endif
  if (ai_surface_nn_init(*network, &params) != true) {
    err = ai_surface_nn_get_error(*network);
  }
  return err;
}


AI_API_ENTRY
ai_buffer* ai_surface_nn_inputs_get(ai_handle network, ai_u16 *n_buffer)
{
  if (network == AI_HANDLE_NULL) {
    network = (ai_handle)&AI_NET_OBJ_INSTANCE;
    AI_NETWORK_OBJ(network)->magic = AI_MAGIC_CONTEXT_TOKEN;
  }
  return ai_platform_inputs_get(network, n_buffer);
}


AI_API_ENTRY
ai_buffer* ai_surface_nn_outputs_get(ai_handle network, ai_u16 *n_buffer)
{
  if (network == AI_HANDLE_NULL) {
    network = (ai_handle)&AI_NET_OBJ_INSTANCE;
    AI_NETWORK_OBJ(network)->magic = AI_MAGIC_CONTEXT_TOKEN;
  }
  return ai_platform_outputs_get(network, n_buffer);
}


AI_API_ENTRY
ai_handle ai_surface_nn_destroy(ai_handle network)
{
  return ai_platform_network_destroy(network);
}


AI_API_ENTRY
ai_bool ai_surface_nn_init(
  ai_handle network, const ai_network_params* params)
{
  ai_network* net_ctx = AI_NETWORK_OBJ(ai_platform_network_init(network, params));
  ai_bool ok = true;

  if (!net_ctx) return false;
  ok &= surface_nn_configure_weights(net_ctx, params);
  ok &= surface_nn_configure_activations(net_ctx, params);

  ok &= ai_platform_network_post_init(network);

  return ok;
}


AI_API_ENTRY
ai_i32 ai_surface_nn_run(
  ai_handle network, const ai_buffer* input, ai_buffer* output)
{
  return ai_platform_network_process(network, input, output);
}


AI_API_ENTRY
ai_i32 ai_surface_nn_forward(ai_handle network, const ai_buffer* input)
{
  return ai_platform_network_process(network, input, NULL);
}



#undef AI_SURFACE_NN_MODEL_SIGNATURE
#undef AI_NET_OBJ_INSTANCE
#undef AI_TOOLS_DATE_TIME
#undef AI_TOOLS_COMPILE_TIME
