Circuit-Digest/EdgeSense/X-CUBE-AI/App/surface_nn_data_params.c

/**
  ******************************************************************************
  * @file    surface_nn_data_params.c
  * @author  AST Embedded Analytics Research Platform
  * @date    2026-09-09T16:02:45+0530
  * @brief   AI Tool Automatic Code Generator for Embedded NN computing
  ******************************************************************************
  * Copyright (c) 2026 STMicroelectronics.
  * All rights reserved.
  *
  * This software is licensed under terms that can be found in the LICENSE file
  * in the root directory of this software component.
  * If no LICENSE file comes with this software, it is provided AS-IS.
  ******************************************************************************
  */

#include "surface_nn_data_params.h"


/**  Activations Section  ****************************************************/
ai_handle g_surface_nn_activations_table[1 + 2] = {
  AI_HANDLE_PTR(AI_MAGIC_MARKER),
  AI_HANDLE_PTR(NULL),
  AI_HANDLE_PTR(AI_MAGIC_MARKER),
};




/**  Weights Section  ********************************************************/
AI_ALIGNED(32)
const ai_u64 s_surface_nn_weights_array_u64[770] = {
  0xbfb9341ac156a869U, 0x3e2a7f483f67a237U, 0xbdc02d8bbe51ccabU, 0xbf087c54bfb986c1U,
  0xc01d6b7ebe1a41a9U, 0x3ef183443fa0b738U, 0x3ddf7a91bf3928ceU, 0x3d32cce03e2c33b9U,
  0x3c1735403e747eb8U, 0xbe046cfe3e99395fU, 0x3ffb2bb43e45e285U, 0xbedb1dc6bf2be1d5U,
  0xbd81dc513e59249dU, 0xbf14ba743f088aeeU, 0xbeaa47863f1575e8U, 0xbdae28b2bedd712fU,
  0xbe3837d73dd15702U, 0xc01435a93f8b93dcU, 0xbdd1d7cd3e8b8fc0U, 0x3e029ef93d3a1b49U,
  0xbe78c8d940013b54U, 0x3eb1d8f7be903a99U, 0xbd4c339c3e684fedU, 0xc0803d43bcbbe4a9U,
  0x3e1bc6ac408596c4U, 0x404c644f3f20a75cU, 0xbbc3fae0beef74b2U, 0x3f76216ebda76e6bU,
  0x3d9eb6123fdb3b41U, 0x3d69814d3e52c9dfU, 0x3db8e6f83e6cc69cU, 0x3e1f903a3e0544d3U,
  0xbd98da9440a2c981U, 0x3fbdafc3bfe64ae7U, 0xbc876218bf257465U, 0x3fa58b553e860ebfU,
  0xbdbe27bbbfe7af34U, 0x407d1a463ef30840U, 0x3dfa36283e9a1c57U, 0xc01162a83dc1c5a3U,
  0x3d08ae1cc0def624U, 0x3ea8ea083dae9e1eU, 0xbd7e61bc3db1c25aU, 0xbd45b93ebc66f2bcU,
  0xbdd1a057bf21a4abU, 0xc022748dbebc30c7U, 0x3cbacee83d452aa1U, 0xbdda081b3ddfaa12U,
  0xbd9581ce3efe6495U, 0xbe938c11bfc098b8U, 0xbccbd818bf11aa5aU, 0x3d592bd43d89b14cU,
  0xbe40d4213dea5fbdU, 0x3bccec80bd48d9caU, 0xbda08160bcacf593U, 0xbe469e803e018b84U,
  0x3d46d578bd2d85e4U, 0x3dc92560be93553dU, 0xbd5780903c15b5a4U, 0xbd3247653d3f0b10U,
  0xbdf92689bb83f87cU, 0x3d0239cbbb0785c0U, 0xbe0575c2be85365bU, 0xbe42e207be0b4832U,
  0x3e12f585400badf6U, 0xbfbb4498bbbe644cU, 0x3e203f343f43b71aU, 0xbfc59ab43c4cc1aaU,
  0x3dd313bfc0c46a57U, 0xbed00174bebda885U, 0x3e406886be96886fU, 0x3f8ea4803da3dc22U,
  0xbcbea4c040227db3U, 0x3f3e7f7cbf9f083cU, 0xbe260e99befb4c42U, 0xbf16e2b7be2a74dbU,
  0xbceca10ac0f71c73U, 0xbf31ec39bf314a8dU, 0x3c11ea503f24cff1U, 0xbeeb69fe3e140d1eU,
  0x3e475981c0851162U, 0x3e3a1596beefbce0U, 0x3e07450c3e8952faU, 0x3f02a56b3d7b6bb2U,
  0xbd4cc333c010d2b2U, 0xbf3e72d93eea79e3U, 0x3a8763803e85a0c0U, 0xbfae9ffbbbdd3492U,
  0x3dbb49a3c12f925eU, 0x3e92631cbf46f4cbU, 0xbdc602adbef2cf4cU, 0xc008cd11bd011609U,
  0x3e728809c06c0527U, 0x3e9bda2b3f337a7fU, 0xbe29ec393e8284a6U, 0x3fba38cabdc9f183U,
  0xbe0d7540c0a20b63U, 0xbf90531a3f7afcd6U, 0xbe246b003f0243eeU, 0xbf443066bdb1494cU,
  0xbdc54e2abf996c38U, 0x3f5c36ddbf7e9778U, 0x3e3e429c3f453d1fU, 0x3df3ce25bd0e0de1U,
  0x3f06c389bf5412a8U, 0xbea3fc9bbeab03f9U, 0x3e367cfebf493002U, 0x3fce734b3d38f8dcU,
  0x3d7c724dbeaa19a4U, 0x3e91f50c3ee22029U, 0x3d8711bc3ef68bb0U, 0xbfbaa7753d725303U,
  0x3e064b883e07e1b3U, 0xbdd0851bbdfce51eU, 0x3d193ad0bd997a6cU, 0x3da838663d27ee81U,
  0x3d9a87e1be207673U, 0xbc06a547bbe2f859U, 0xbd81363abdc3b6d8U, 0xbe6a26d8bde24884U,
  0xbe647eda3e0e28e4U, 0x3e0dee0abe18db32U, 0xbe0a06eabec8bd88U, 0xbeb2e8f93dea3b09U,
  0xbc87c938bd9698e4U, 0x3d67da08be1c5b66U, 0x3e0a02303e2e01b8U, 0x3c3b3cf0bc6e6cd0U,
  0xbc8fbaf8bdffb1e2U, 0x3e34b6aebd2ab9dcU, 0x3d9d1160be3d071dU, 0xbb8c09203de27f70U,
  0x3d8d75b0bdd9ba34U, 0xbdf51069be15762eU, 0x3e022006be01ce06U, 0xbe4e149abd9bf646U,
  0x3e81190ec00df92fU, 0xc033324ec0a4aa58U, 0xbdda22ff3ff4196bU, 0x3bca852cbe2e782cU,
  0xbdeed1f83f763c21U, 0xc00d5222c004c695U, 0x3d833d4cbf69b85aU, 0xbea15ee23e12caefU,
  0x3c8b66d4bf24b009U, 0x3fc35de5bc8fab6dU, 0xbc5335403eedc3e2U, 0x3f4b95a73de03173U,
  0x3dd514fcbe43a6afU, 0xbb8e58e03d289984U, 0x3e0ce3603dabdd8cU, 0xbe2bf9f83db86f74U,
  0xbd981bf23dd3cb68U, 0xbe4233cfbde02c6cU, 0x3d7468b0bd3e2b74U, 0xbca70220bc162620U,
  0x3cd52530be0526ccU, 0x3dc953503e3ea57aU, 0x3dc82e90bd93fd3aU, 0xbe2a75fb3dd36054U,
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
};


ai_handle g_surface_nn_weights_table[1 + 2] = {
  AI_HANDLE_PTR(AI_MAGIC_MARKER),
  AI_HANDLE_PTR(s_surface_nn_weights_array_u64),
  AI_HANDLE_PTR(AI_MAGIC_MARKER),
};
